RedCommissary/display-tft-3.5/firmware/source/application/inc/main.h

/********************************************************************************
 * project     HMI panel of the MCU STM32F401CCU6 and TFT ILI9488 (SPI)         *
 *                                                                              *
 * file        main.h                                                    *
 * author      @RedCommissary                                                   *
 * date        10.02.2021                                                       *
 *                                                                              *
 ********************************************************************************/

#pragma once

/********************************************************************************
 * Include 
 ********************************************************************************/

#include "Application.h"
